ruffner/ee572/project/Images/comptarget.png

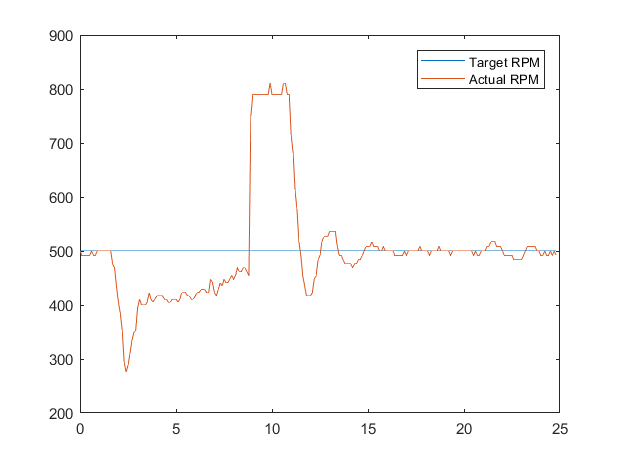
project/Images/comptarget.png
