ruffner/ee572/project/Images/rampfollow.png

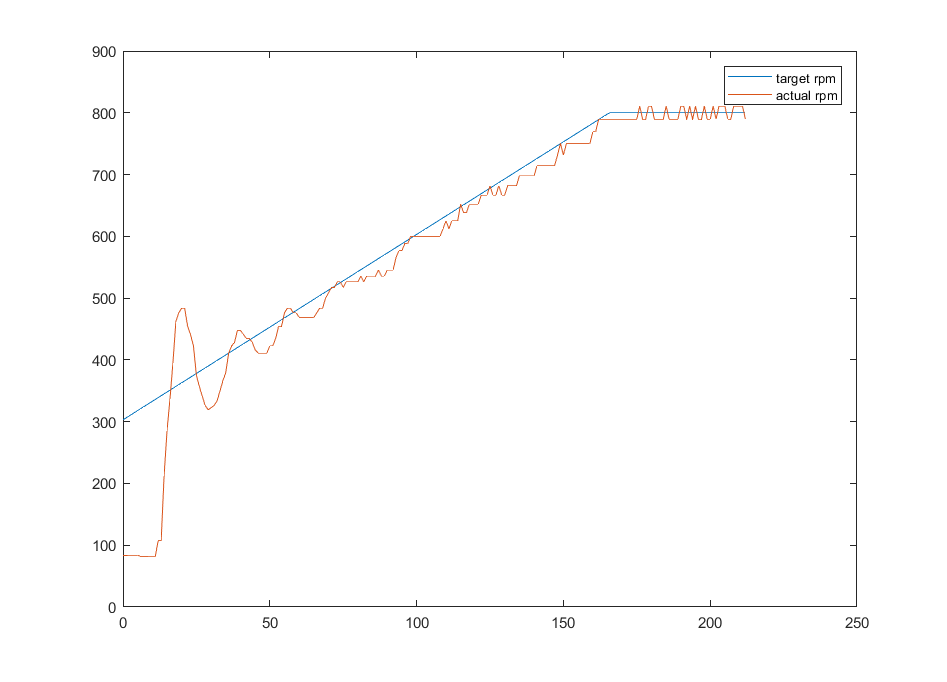
project/Images/rampfollow.png
