ruffner/ee572/project/Images/targvsact.png

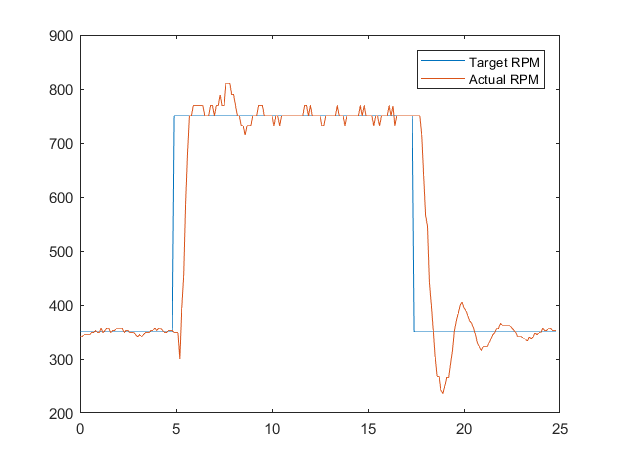
project/Images/targvsact.png
