ruffner/ee572/project/Images/wkyk.png

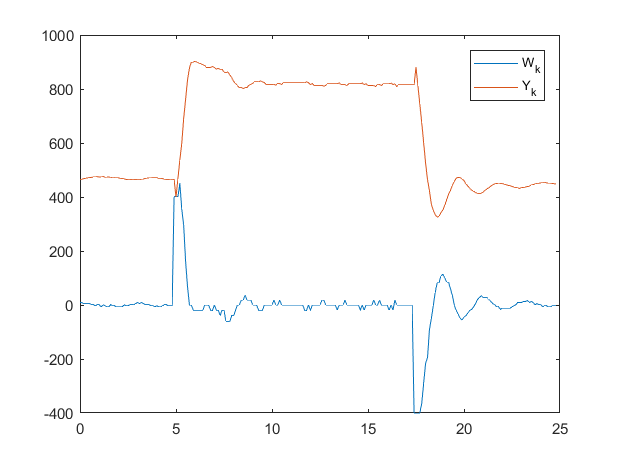
project/Images/wkyk.png
