ruffner/ee572/project/Images/step_after_comp.JPG

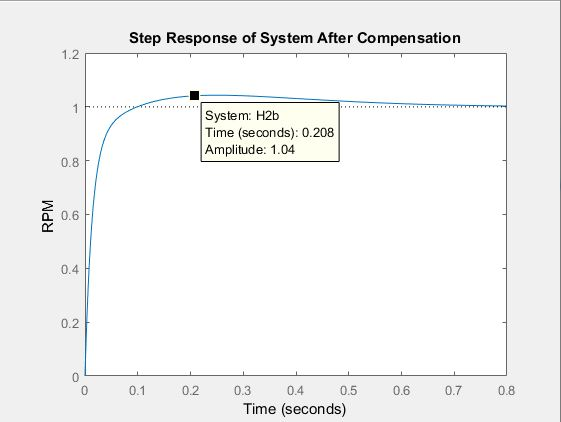
project/Images/step_after_comp.JPG
