ruffner/ee572/project/Images/step_before_comp.jpg

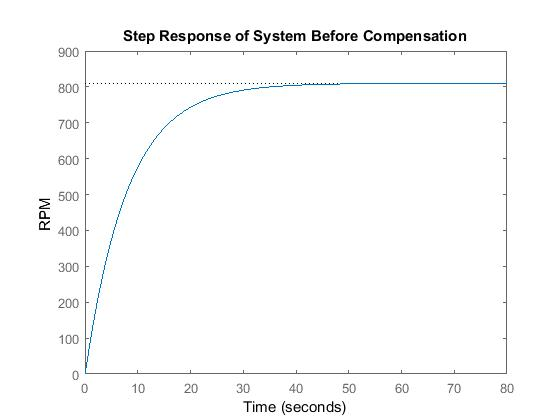
project/Images/step_before_comp.jpg
