ruffner/ee572/project/calibration/speedfit.png

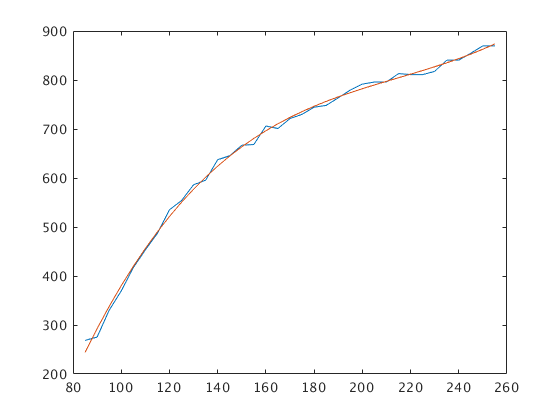
project/calibration/speedfit.png
