ruffner/ee572/project/calibration/speedgrade.png

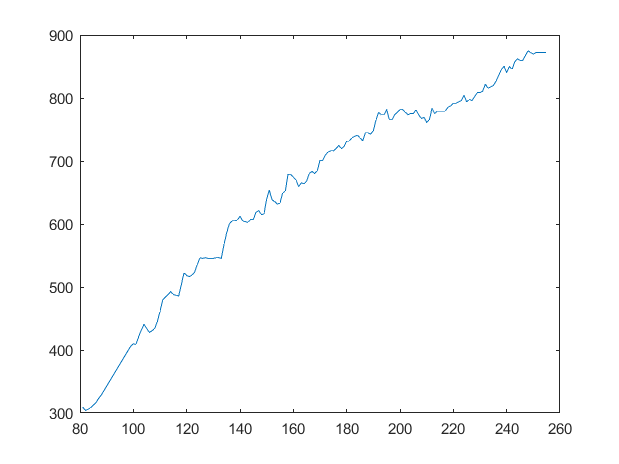
project/calibration/speedgrade.png
